mp-se/kegmon2/src_docs/source/images/ui_device_events.png

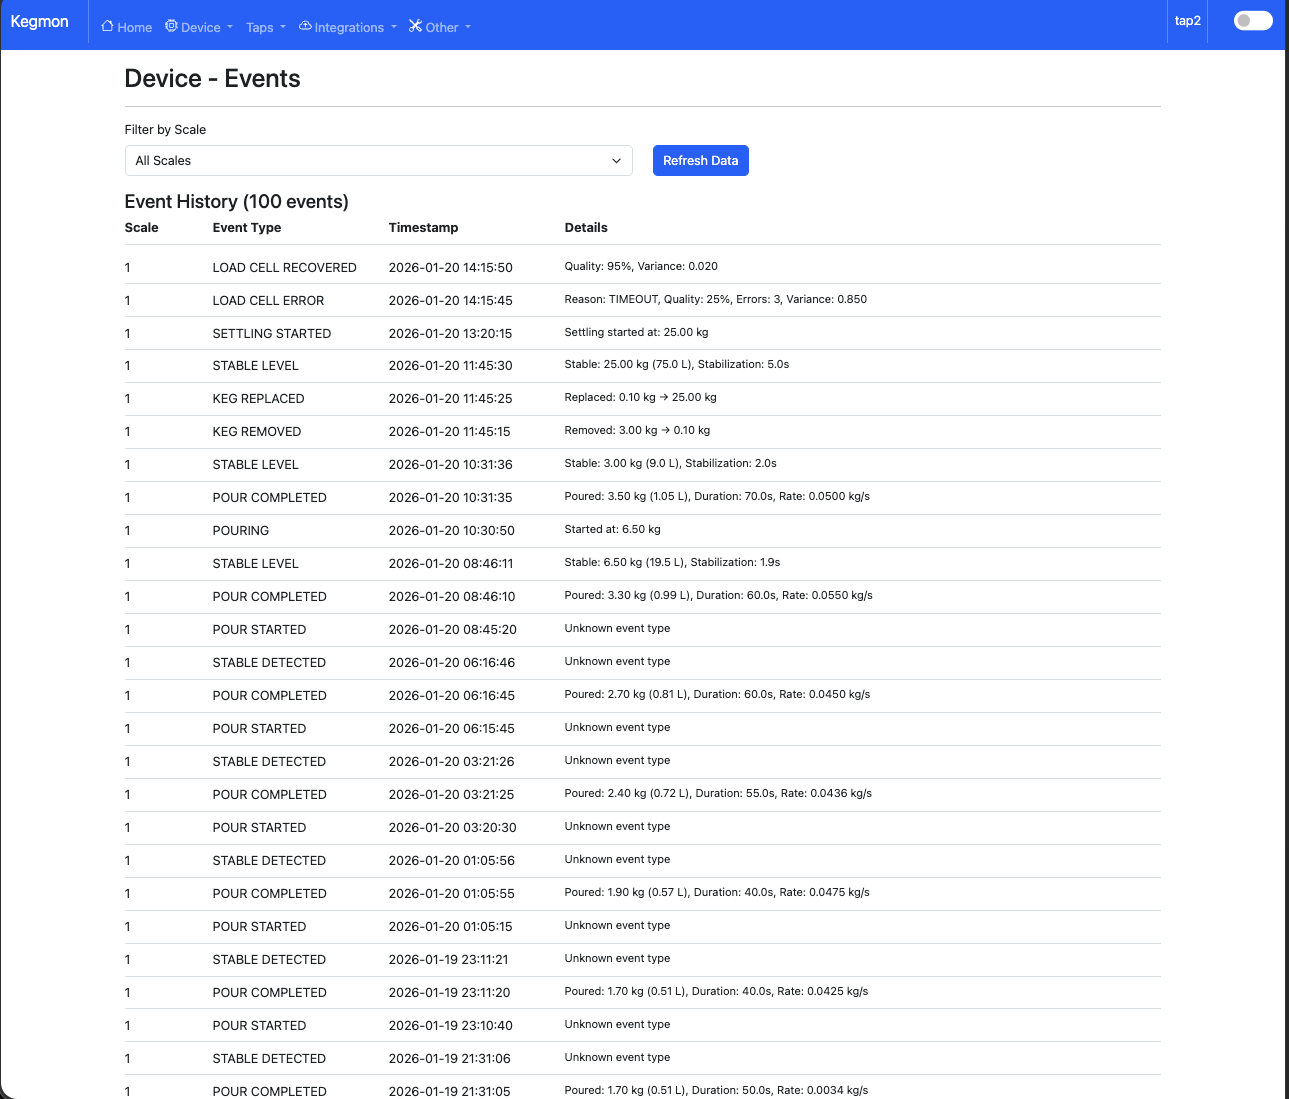
src_docs/source/images/ui_device_events.png
