mp-se/kegmon2/src_docs/source/images/ui_other_about.png

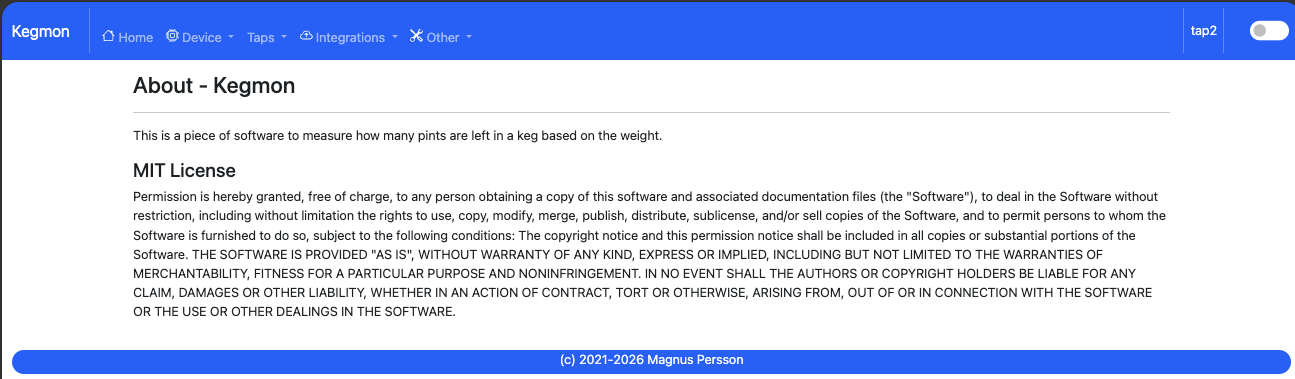
src_docs/source/images/ui_other_about.png
