mp-se/kegmon2/src/kegwebhandler.cpp

/*
 * KegMon
 * Copyright (c) 2022-2026 Magnus
 *
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
 * Alternatively, this software may be used under the terms of a
 * commercial license. See LICENSE_COMMERCIAL for details.
 *
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
 */
#include <DallasTemperature.h>
#include <OneWire.h>
#include <esp_chip_info.h>
#include <freertos/FreeRTOS.h>

#include <changedetection.hpp>
#include <kegpush.hpp>
#include <kegwebhandler.hpp>
#include <main.hpp>
#include <scale.hpp>
#include <sdcard_mmc.hpp>
#include <sdcard_sd.hpp>
#include <temp_mgr.hpp>
#include <uptime.hpp>
#include <utils.hpp>
#include <weightvolume.hpp>

// Configuration or api params
constexpr auto PARAM_APP_VER = "app_ver";
constexpr auto PARAM_APP_BUILD = "app_build";
constexpr auto PARAM_PLATFORM = "platform";
constexpr auto PARAM_BOARD = "board";
constexpr auto PARAM_CHIP_ID = "chip_id";
constexpr auto PARAM_FIRMWARE_FILE = "firmware_file";
constexpr auto PARAM_FEATURE_NO_SCALES = "no_scales";
constexpr auto PARAM_FEATURE_TFT = "tft";

// Other values
constexpr auto PARAM_TOTAL_HEAP = "total_heap";
constexpr auto PARAM_FREE_HEAP = "free_heap";
constexpr auto PARAM_IP = "ip";
constexpr auto PARAM_ADRESS = "adress";
constexpr auto PARAM_FAMILY = "family";
constexpr auto PARAM_CHIP = "chip";
constexpr auto PARAM_REVISION = "revision";
constexpr auto PARAM_CORES = "cores";
constexpr auto PARAM_FEATURES = "features";
constexpr auto PARAM_WIFI_SETUP = "wifi_setup";
constexpr auto PARAM_ONEWIRE = "onewire";

constexpr auto PARAM_UPTIME_SECONDS = "uptime_seconds";
constexpr auto PARAM_UPTIME_MINUTES = "uptime_minutes";
constexpr auto PARAM_UPTIME_HOURS = "uptime_hours";
constexpr auto PARAM_UPTIME_DAYS = "uptime_days";

// Temperature sensor parameters
constexpr auto PARAM_SENSORS = "sensors";
constexpr auto PARAM_SENSOR_INDEX = "index";
constexpr auto PARAM_SENSOR_ID = "id";
constexpr auto PARAM_SENSOR_TEMPERATURE = "temperature";

// Push status
constexpr auto PARAM_HOMEASSISTANT = "ha";
constexpr auto PARAM_BARHELPER = "barhelper";
constexpr auto PARAM_BREWSPY = "brewspy";
constexpr auto PARAM_BREWLOGGER = "brewlogger";
constexpr auto PARAM_PUSH_USED = "push_used";
constexpr auto PARAM_PUSH_AGE = "push_age";
constexpr auto PARAM_PUSH_STATUS = "push_status";
constexpr auto PARAM_PUSH_CODE = "push_code";
constexpr auto PARAM_PUSH_RESPONSE = "push_response";

// Scale parameters
constexpr auto PARAM_SCALE_INDEX = "index";
constexpr auto PARAM_STATE = "state";
constexpr auto PARAM_STABLE_WEIGHT = "stable_weight";
constexpr auto PARAM_POURING_VOLUME = "pouring_volume";
constexpr auto PARAM_LAST_POUR_VOLUME = "last_pour_volume";
constexpr auto PARAM_CONNECTED = "connected";
constexpr auto PARAM_SAMPLING_RATE = "sampling_rate";
constexpr auto PARAM_SIGNAL_QUALITY = "signal_quality";
constexpr auto PARAM_WEIGHT = "weight";
constexpr auto PARAM_SCALE = "scale_index";
constexpr auto PARAM_SCALE_BUSY = "scale_busy";
constexpr auto PARAM_RECENT_EVENTS = "recent_events";
constexpr auto PARAM_TYPE = "type";
constexpr auto PARAM_UNIT = "unit";
constexpr auto PARAM_TIMESTAMP_MS = "timestamp_ms";
constexpr auto PARAM_NAME = "name";
constexpr auto PARAM_DATA = "data";
constexpr auto PARAM_STABLE_VOLUME = "stable_volume";
constexpr auto PARAM_DURATION_MS = "duration_ms";
constexpr auto PARAM_PRE_WEIGHT = "pre_weight";
constexpr auto PARAM_POST_WEIGHT = "post_weight";
constexpr auto PARAM_VOLUME = "volume";
constexpr auto PARAM_AVG_SLOPE = "avg_slope";
constexpr auto PARAM_PREVIOUS_WEIGHT = "previous_weight";
constexpr auto PARAM_CURRENT_WEIGHT = "current_weight";
constexpr auto PARAM_EVENT_STARTUP = "startup";
constexpr auto PARAM_EVENT_SETTLING_STARTED = "settling_started";
constexpr auto PARAM_EVENT_STABLE_LEVEL = "stable_level";
constexpr auto PARAM_EVENT_POURING = "pouring";
constexpr auto PARAM_EVENT_WEIGHT_CHANGE_DETECTED = "weight_change_detected";
constexpr auto PARAM_EVENT_POUR_COMPLETED = "pour_completed";
constexpr auto PARAM_EVENT_KEG_REMOVED = "keg_removed";
constexpr auto PARAM_EVENT_KEG_REPLACED = "keg_replaced";
constexpr auto PARAM_EVENT_KEG_ABSENT_TIMEOUT = "keg_absent_timeout";
constexpr auto PARAM_EVENT_INVALID_WEIGHT = "invalid_weight";
constexpr auto PARAM_EVENT_LOAD_CELL_ERROR = "load_cell_error";
constexpr auto PARAM_EVENT_LOAD_CELL_RECOVERED = "load_cell_recovered";
constexpr auto PARAM_EVENT_SENSOR_RECOVERED = "sensor_recovered";
constexpr auto PARAM_EVENT_CALIBRATION_NEEDED = "calibration_needed";
constexpr auto PARAM_EVENT_CALIBRATION_COMPLETE = "calibration_complete";
constexpr auto PARAM_SIGNAL_REASON = "reason";
constexpr auto PARAM_VARIANCE = "variance";
constexpr auto PARAM_CONSECUTIVE_ERRORS = "consecutive_errors";
constexpr auto PARAM_INVALID_WEIGHT = "weight";
constexpr auto PARAM_MIN_VALID_WEIGHT = "min_valid_weight";
constexpr auto PARAM_MAX_VALID_WEIGHT = "max_valid_weight";
constexpr auto PARAM_SD_MOUNTED = "sd_mounted";
constexpr auto PARAM_SD = "sd";

// Forward declaration
static void eventToJson(const ChangeDetectionEvent &event, JsonObject obj);
constexpr auto PARAM_SCALE_WEIGHT = "scale_weight";
constexpr auto PARAM_SCALE_RAW = "scale_raw";
constexpr auto PARAM_GLASS = "glass";

#if defined(ENABLE_MMC)
extern SdCardMMC mySdStorage;
#elif defined(ENABLE_SD)
extern SdCardSD mySdStorage;
#endif

KegWebHandler::KegWebHandler(KegConfig *config) : BaseWebServer(config) {
  _config = config;
}

void KegWebHandler::setupWebHandlers() {
  Log.notice(F("WEB : Setting up keg web handlers." CR));

  BaseWebServer::setupWebHandlers();

  MDNS.addService("kegmon", "tcp", 80);

  // TODO(mpse) : Serve static files from SD card
  // Note! For the async implementation the order matters
  // _server->serveStatic("/levels2", LittleFS, LEVELS_FILENAME2);
  // _server->serveStatic("/levels", LittleFS, LEVELS_FILENAME);
  // _server->serveStatic("/startup", LittleFS, STARTUP_FILENAME);

  AsyncCallbackJsonWebHandler *handler;
  handler = new AsyncCallbackJsonWebHandler(
      "/api/scale/tare",
      std::bind(&KegWebHandler::webScaleTare, this, std::placeholders::_1,
                std::placeholders::_2));
  _server->addHandler(handler);
  handler = new AsyncCallbackJsonWebHandler(
      "/api/scale/factor",
      std::bind(&KegWebHandler::webScaleFactor, this, std::placeholders::_1,
                std::placeholders::_2));
  _server->addHandler(handler);
  _server->on("/api/scale", HTTP_GET, [this](AsyncWebServerRequest *request) {
    this->webScale(request);
  });
  _server->on("/api/feature", HTTP_GET, [this](AsyncWebServerRequest *request) {
    this->webFeature(request);
  });
  _server->on("/api/config", HTTP_GET, [this](AsyncWebServerRequest *request) {
    this->webConfigGet(request);
  });
  handler = new AsyncCallbackJsonWebHandler(
      "/api/config", std::bind(&KegWebHandler::webConfigPost, this,
                               std::placeholders::_1, std::placeholders::_2));
  _server->addHandler(handler);
  _server->on("/api/statistic/clear", HTTP_GET,
              [this](AsyncWebServerRequest *request) {
                this->webStatisticClear(request);
              });
  _server->on(
      "/api/statistic", HTTP_GET,
      [this](AsyncWebServerRequest *request) { this->webStatistic(request); });
  _server->on("/api/status", HTTP_GET, [this](AsyncWebServerRequest *request) {
    this->webStatus(request);
  });
  handler = new AsyncCallbackJsonWebHandler(
      "/api/brewspy/tap",
      std::bind(&KegWebHandler::webHandleBrewspy, this, std::placeholders::_1,
                std::placeholders::_2));
  _server->addHandler(handler);
  _server->on("/api/hardware/status", HTTP_GET,
              [this](AsyncWebServerRequest *request) {
                this->webHardwareScanStatus(request);
              });
  _server->on("/api/hardware", HTTP_GET,
              [this](AsyncWebServerRequest *request) {
                this->webHardwareScan(request);
              });
  _server->on("/api/factory", HTTP_GET, [this](AsyncWebServerRequest *request) {
    this->webHandleFactoryDefaults(request);
  });
  handler = new AsyncCallbackJsonWebHandler(
      "/api/sd", std::bind(&KegWebHandler::webHandleSecureDigital, this,
                           std::placeholders::_1, std::placeholders::_2));
  _server->addHandler(handler);
#if defined(ENABLE_MMC) || defined(ENABLE_SD)
  _server->serveStatic("/sd", mySdStorage.getFS(), "/");
#endif  
}

void KegWebHandler::webHandleSecureDigital(AsyncWebServerRequest *request,
                                           JsonVariant &json) {
  if (!isAuthenticated(request)) {
    return;
  }

  Log.notice(F("WEB : webServer callback for /api/sd." CR));
#if defined(ENABLE_MMC) || defined(ENABLE_SD)
  JsonObject obj = json.as<JsonObject>();

  if (!obj[PARAM_COMMAND].isNull()) {
    if (obj[PARAM_COMMAND] == String("dir")) {
      Log.notice(F("WEB : File system listing requested." CR));
      AsyncJsonResponse *response = new AsyncJsonResponse(false);
      JsonObject obj = response->getRoot().as<JsonObject>();

      obj[PARAM_TOTAL] = mySdStorage.totalBytes();
      obj[PARAM_USED] = mySdStorage.usedBytes();
      obj[PARAM_FREE] = mySdStorage.totalBytes() - mySdStorage.usedBytes();

      File root = mySdStorage.open("/", FILE_READ);
      File f = root.openNextFile();
      int i = 0;

      JsonArray arr = obj[PARAM_FILES].to<JsonArray>();
      while (f) {
        Log.notice(F("WEB : %s." CR), f.name());
        if (!String(f.name()).startsWith(
                ".")) {  // Ignore files with . (hidden files)
          arr[i][PARAM_FILE] = "/" + String(f.name());
          arr[i][PARAM_SIZE] = static_cast<int>(f.size());
          i++;
        }
        f = root.openNextFile();
      }
      f.close();
      root.close();

      response->setLength();
      request->send(response);
    } else if (obj[PARAM_COMMAND] == String("del")) {
      Log.notice(F("WEB : File system delete requested." CR));

      if (!obj[PARAM_FILE].isNull()) {
        String f = obj[PARAM_FILE];
        mySdStorage.remove(f);
        request->send(200);
      } else {
        request->send(400);
      }
    } else {
      Log.warning(F("WEB : Unknown file system command." CR));
      request->send(400);
    }
  } else {
    Log.warning(F("WEB : Unknown file system command." CR));
    request->send(400);
  }
#endif
}

void KegWebHandler::webConfigGet(AsyncWebServerRequest *request) {
  if (!isAuthenticated(request)) {
    return;
  }

  Log.notice(F("WEB : webServer callback for /api/config(read)." CR));
  AsyncJsonResponse *response = new AsyncJsonResponse(false);
  JsonObject obj = response->getRoot().as<JsonObject>();
  myConfig.createJson(obj);
  response->setLength();
  request->send(response);
}

void KegWebHandler::webHandleFactoryDefaults(AsyncWebServerRequest *request) {
  if (!isAuthenticated(request)) {
    return;
  }

  Log.notice(F("WEB : webServer callback for /api/factory." CR));
  myConfig.saveFileWifiOnly();
  LittleFS.remove(ERR_FILENAME);
  LittleFS.end();
  Log.notice(F("WEB : Deleted files in filesystem, rebooting." CR));

  AsyncJsonResponse *response = new AsyncJsonResponse(false);
  JsonObject obj = response->getRoot().as<JsonObject>();
  obj[PARAM_SUCCESS] = true;
  obj[PARAM_MESSAGE] = "Factory reset completed, rebooting";
  response->setLength();
  request->send(response);
  delay(500);
  ESP_RESET();
}

void KegWebHandler::webConfigPost(AsyncWebServerRequest *request,
                                  JsonVariant &json) {
  if (!isAuthenticated(request)) {
    return;
  }

  Log.notice(F("WEB : webServer callback for /api/config(write)." CR));
  JsonObject obj = json.as<JsonObject>();
  myConfig.parseJson(obj);
  obj.clear();
  myConfig.saveFile();

  AsyncJsonResponse *response = new AsyncJsonResponse(false);
  obj = response->getRoot().as<JsonObject>();
  obj[PARAM_SUCCESS] = true;
  obj[PARAM_MESSAGE] = "Configuration updated";
  response->setLength();
  request->send(response);
}

void KegWebHandler::webHandleBrewspy(AsyncWebServerRequest *request,
                                     JsonVariant &json) {
  if (!isAuthenticated(request)) {
    return;
  }

  JsonObject obj = json.as<JsonObject>();
  AsyncJsonResponse *response = new AsyncJsonResponse(false);
  JsonObject obj2 = response->getRoot().as<JsonObject>();
  myPush.requestTapInfoFromBrewspy(obj2, obj[PARAM_TOKEN]);
  response->setLength();
  request->send(response);
}

void KegWebHandler::webScale(AsyncWebServerRequest *request) {
  if (!isAuthenticated(request)) {
    return;
  }

  Log.notice(F("WEB : webServer callback /api/scale." CR));

  AsyncJsonResponse *response = new AsyncJsonResponse(false);
  JsonObject obj = response->getRoot().as<JsonObject>();
  obj[PARAM_WEIGHT_UNIT] = myConfig.getWeightUnit();
  obj[PARAM_VOLUME_UNIT] = myConfig.getVolumeUnit();
  obj[PARAM_TEMP_UNIT] = String(myConfig.getTempUnit());

  obj[PARAM_SCALE_BUSY] = myScale.isScheduleRunning();

  // Return array of all scales with current state
  JsonArray scales_array = obj[PARAM_SCALES].to<JsonArray>();
  for (int i = 0; i < MAX_SCALES; i++) {
    UnitIndex idx = static_cast<UnitIndex>(i);
    JsonObject scale = scales_array.add<JsonObject>();

    scale[PARAM_SCALE_INDEX] = i;
    scale[PARAM_CONNECTED] = myScale.isConnected(idx);

    scale[PARAM_SCALE_FACTOR] = myConfig.getScaleFactor(idx);
    scale[PARAM_SCALE_OFFSET] = myConfig.getScaleOffset(idx);

    // Add detected sampling rate (measured from Data Ready signal timing)
    if (myScale.isConnected(idx)) {
      uint8_t detected_rate = myScale.getSamplingRate(idx);
      if (detected_rate > 0) {
        scale[PARAM_SAMPLING_RATE] = detected_rate;
      }

      // Add signal quality for load cell connection monitoring
      uint8_t quality = myChangeDetection.getSignalQuality(idx);
      scale[PARAM_SIGNAL_QUALITY] = quality;
    }

    // Only add other data if scale is connected
    if (myScale.isConnected(idx)) {
      scale[PARAM_STATE] = myChangeDetection.getStateString(idx);

      if (!isnan(myChangeDetection.getStableWeight(idx))) {
        scale[PARAM_STABLE_WEIGHT] = myChangeDetection.getStableWeight(idx);
      }
      scale[PARAM_SCALE_RAW] = myScale.readLastRaw(idx);
    }
  }

  response->setLength();
  request->send(response);
}

void KegWebHandler::webScaleTare(AsyncWebServerRequest *request,
                                 JsonVariant &json) {
  if (!isAuthenticated(request)) {
    return;
  }

  JsonObject obj = json.as<JsonObject>();
  int i = obj[PARAM_SCALE].as<int>();

  if (i < 0 || i >= MAX_SCALES) {
    request->send(400);
    return;
  }

  Log.notice(F("WEB : webServer callback /api/scale/tare." CR));
  myScale.scheduleTare((UnitIndex)i);

  AsyncJsonResponse *response = new AsyncJsonResponse(false);
  JsonObject obj2 = response->getRoot().as<JsonObject>();
  obj2[PARAM_SUCCESS] = true;
  obj2[PARAM_MESSAGE] = "Scale tare schedule";
  response->setLength();
  request->send(response);
}

void KegWebHandler::webScaleFactor(AsyncWebServerRequest *request,
                                   JsonVariant &json) {
  if (!isAuthenticated(request)) {
    return;
  }

  JsonObject obj = json.as<JsonObject>();
  UnitIndex idx;
  float weight = obj[PARAM_WEIGHT].as<float>();

  int i = obj[PARAM_SCALE].as<int>();

  if (i < 0 || i >= MAX_SCALES) {
    request->send(400);
    return;
  }

  Log.notice(
      F("WEB : webServer callback /api/scale/factor, weight=%Fkg [%d]." CR),
      weight, i);

  myScale.scheduleFindFactor((UnitIndex)i, weight);

  AsyncJsonResponse *response = new AsyncJsonResponse(false);
  JsonObject obj2 = response->getRoot().as<JsonObject>();
  obj2[PARAM_SUCCESS] = true;
  obj2[PARAM_MESSAGE] = "Scale tare is scheduled";
  response->setLength();
  request->send(response);
}

void KegWebHandler::webFeature(AsyncWebServerRequest *request) {
  Log.notice(F("WEB : webServer callback /api/feature." CR));

  AsyncJsonResponse *response = new AsyncJsonResponse(false);
  JsonObject obj = response->getRoot().as<JsonObject>();

#if defined(ESP32S3)
  obj[PARAM_PLATFORM] = "esp32s3";
#else
#error "Undefined target"
#endif
#if defined(BOARD)
  obj[PARAM_BOARD] = BOARD;
#else
  obj[PARAM_BOARD] = "UNDEFINED";
#endif
  obj[PARAM_APP_VER] = CFG_APPVER;
  obj[PARAM_APP_BUILD] = CFG_GITREV;
  obj[PARAM_CHIP_ID] = String(ESP.getEfuseMac(), HEX);
  obj[PARAM_FIRMWARE_FILE] = CFG_FILENAMEBIN;

  int noScales = 0;
  for (int i = 0; i < MAX_SCALES; i++) {
    if (myScale.isConnected(static_cast<UnitIndex>(i))) noScales = i + 1;
  }
  obj[PARAM_FEATURE_NO_SCALES] = noScales;

#if defined(ENABLE_TFT)
  obj[PARAM_FEATURE_TFT] = true;
#else
  obj[PARAM_FEATURE_TFT] = false;
#endif
#if defined(ENABLE_MMC) || defined(ENABLE_SD)
  obj[PARAM_SD] = true;
#else
  obj[PARAM_SD] = false;
#endif
  response->setLength();
  request->send(response);
}

void KegWebHandler::webStatus(AsyncWebServerRequest *request) {
  Log.notice(F("WEB : webServer callback /api/status." CR));

  AsyncJsonResponse *response = new AsyncJsonResponse(false);
  JsonObject obj = response->getRoot().as<JsonObject>();
  obj[PARAM_MDNS] = myConfig.getMDNS();
  obj[PARAM_ID] = myConfig.getID();
  obj[PARAM_RSSI] = WiFi.RSSI();
  obj[PARAM_SSID] = myConfig.getWifiSSID(0);
  obj[PARAM_WEIGHT_UNIT] = myConfig.getWeightUnit();
  obj[PARAM_VOLUME_UNIT] = myConfig.getVolumeUnit();
  obj[PARAM_TEMP_FORMAT] = String(myConfig.getTempFormat());

  obj[PARAM_UPTIME_SECONDS] = myUptime.getSeconds();
  obj[PARAM_UPTIME_MINUTES] = myUptime.getMinutes();
  obj[PARAM_UPTIME_HOURS] = myUptime.getHours();
  obj[PARAM_UPTIME_DAYS] = myUptime.getDays();

  obj[PARAM_SCALE_BUSY] = myScale.isScheduleRunning();

#if defined(ENABLE_MMC) || defined(ENABLE_SD)
  obj[PARAM_SD_MOUNTED] = mySdStorage.hasCard();
#else
  obj[PARAM_SD_MOUNTED] = false;
#endif

  // Return array of all scales with current state
  JsonArray scales_array = obj[PARAM_SCALES].to<JsonArray>();
  for (int i = 0; i < MAX_SCALES; i++) {
    UnitIndex idx = static_cast<UnitIndex>(i);
    JsonObject scale = scales_array.add<JsonObject>();

    scale[PARAM_SCALE_INDEX] = i;
    scale[PARAM_CONNECTED] = myScale.isConnected(idx);
    // scale[PARAM_SCALE_FACTOR] = myConfig.getScaleFactor(idx);
    // scale[PARAM_SCALE_OFFSET] = myConfig.getScaleOffset(idx);

    // Add detected sampling rate (measured from Data Ready signal timing)
    uint8_t detected_rate = myScale.getSamplingRate(idx);
    if (detected_rate > 0) {
      scale[PARAM_SAMPLING_RATE] = detected_rate;
    }

    // Only add other data if scale is connected
    if (myScale.isConnected(idx)) {
      scale[PARAM_STATE] = myChangeDetection.getStateString(idx);

      // Weight and volume data (in kg and liters)
      float stableWeight = myChangeDetection.getStableWeight(idx);
      if (!isnan(stableWeight)) {
        scale[PARAM_STABLE_WEIGHT] =
            serialized(String(stableWeight, 4));
      }

      float stableVolume = myChangeDetection.getStableVolume(idx);
      if (!isnan(stableVolume)) {
        scale[PARAM_STABLE_VOLUME] =
            serialized(String(stableVolume, 4));
      }

      float pouringVolume = myChangeDetection.getPouringVolume(idx);
      scale[PARAM_POURING_VOLUME] =
          serialized(String(pouringVolume, 4));

      float lastPourVolume = myChangeDetection.getLastPourVolume(idx);
      scale[PARAM_LAST_POUR_VOLUME] =
          serialized(String(lastPourVolume, 4));

      // Keg volume in liters
      float keg_volume_liters = myConfig.getKegVolume(idx);
      scale[PARAM_KEG_VOLUME] =
          serialized(String(keg_volume_liters, 4));

      // Calculate number of glasses (glass volume from config)
      float glass_volume_liters = myConfig.getGlassVolume(idx);
      if (glass_volume_liters > 0.0f && !isnan(stableVolume) &&
          stableVolume > 0.0f) {
        // Use stableVolume directly (both in liters)
        scale[PARAM_GLASS] =
            serialized(String(stableVolume / glass_volume_liters, 1));
      }

      // scale[PARAM_SCALE_RAW] = myScale.readLastRaw(idx);
    }
  }

  // Return array of all temperature sensors
  if (myTemp.hasSensor()) {
    JsonArray sensors_array = obj[PARAM_SENSORS].to<JsonArray>();
    int sensor_count = myTemp.getSensorCount();
    for (int i = 0; i < sensor_count; i++) {
      JsonObject sensor = sensors_array.add<JsonObject>();

      sensor[PARAM_SENSOR_INDEX] = i;
      sensor[PARAM_SENSOR_ID] = myTemp.getSensorId(i);

      float temp_c = myTemp.getLastTempC(i);
      if (!isnan(temp_c)) {
        sensor[PARAM_SENSOR_TEMPERATURE] = serialized(String(temp_c, 2));
      }
    }
  }

  obj[PARAM_TOTAL_HEAP] = ESP.getHeapSize();
  obj[PARAM_FREE_HEAP] = ESP.getFreeHeap();
  obj[PARAM_IP] = WiFi.localIP().toString();
  obj[PARAM_WIFI_SETUP] = (runMode == RunMode::wifiSetupMode) ? true : false;

  // Home Assistant
  if (myConfig.hasTargetMqtt()) {
    JsonObject o = obj[PARAM_HOMEASSISTANT].to<JsonObject>();
    HomeAssist *ha = myPush.getHomeAssist();
    o[PARAM_PUSH_AGE] =
        abs(static_cast<int32_t>((millis() - ha->getLastTimeStamp())));
    o[PARAM_PUSH_STATUS] = ha->getLastStatus();
    o[PARAM_PUSH_CODE] = ha->getLastError();
    o[PARAM_PUSH_RESPONSE] = "";
    o[PARAM_PUSH_USED] = ha->hasRun();
  }

  // Bar helper
  if (strlen(myConfig.getBarhelperApiKey()) > 0) {
    JsonObject o = obj[PARAM_BARHELPER].to<JsonObject>();
    Barhelper *bar = myPush.getBarHelper();
    o[PARAM_PUSH_AGE] =
        abs(static_cast<int32_t>((millis() - bar->getLastTimeStamp())));
    o[PARAM_PUSH_STATUS] = bar->getLastStatus();
    o[PARAM_PUSH_CODE] = bar->getLastError();
    o[PARAM_PUSH_RESPONSE] = bar->getLastResponse();
    o[PARAM_PUSH_USED] = bar->hasRun();
  }

  // Brewlogger helper
  if (strlen(myConfig.getBrewLoggerUrl()) > 0) {
    JsonObject o = obj[PARAM_BREWLOGGER].to<JsonObject>();
    BrewLogger *blog = myPush.getBrewLogger();
    o[PARAM_PUSH_AGE] =
        abs(static_cast<int32_t>((millis() - blog->getLastTimeStamp())));
    o[PARAM_PUSH_STATUS] = blog->getLastStatus();
    o[PARAM_PUSH_CODE] = blog->getLastError();
    o[PARAM_PUSH_RESPONSE] = blog->getLastResponse();
    o[PARAM_PUSH_USED] = blog->hasRun();
  }

  // Brewspy
  if (strlen(myConfig.getBrewspyToken(UnitIndex::U1)) > 0 ||
      strlen(myConfig.getBrewspyToken(UnitIndex::U2)) > 0) {
    JsonObject o = obj[PARAM_BREWSPY].to<JsonObject>();
    Brewspy *brew = myPush.getBrewspy();
    o[PARAM_PUSH_AGE] =
        abs(static_cast<int32_t>((millis() - brew->getLastTimeStamp())));
    o[PARAM_PUSH_STATUS] = brew->getLastStatus();
    o[PARAM_PUSH_CODE] = brew->getLastError();
    o[PARAM_PUSH_RESPONSE] = brew->getLastResponse();
    o[PARAM_PUSH_USED] = brew->hasRun();
  }

  // Recent events from change detection
  {
    ChangeDetectionEvent recentEvents[RECENT_EVENTS_SIZE];
    size_t eventCount = 0;
    this->getRecentEvents(recentEvents, eventCount);

    JsonArray events_array = obj[PARAM_RECENT_EVENTS].to<JsonArray>();
    for (size_t i = 0; i < eventCount; i++) {
      JsonObject event_obj = events_array.add<JsonObject>();
      eventToJson(recentEvents[i], event_obj);
    }
  }

  response->setLength();
  request->send(response);
}

void KegWebHandler::webStatistic(AsyncWebServerRequest *request) {
  if (!isAuthenticated(request)) {
    return;
  }

  Log.notice(F("WEB : webServer callback /api/stability." CR));

  AsyncJsonResponse *response = new AsyncJsonResponse(false);
  JsonObject obj = response->getRoot().as<JsonObject>();

  // Level statistics array (ChangeDetection v2 statistics)
  JsonArray level_statistics = obj["level_statistics"].to<JsonArray>();
  for (int i = 0; i < MAX_SCALES; i++) {
    UnitIndex idx = static_cast<UnitIndex>(i);
    JsonObject stat = level_statistics.add<JsonObject>();

    // Basic scale info
    stat[PARAM_SCALE_INDEX] = i;
    stat[PARAM_CONNECTED] = myScale.isConnected(idx);
    stat[PARAM_STATE] = myChangeDetection.getStateString(idx);
    stat["confidence"] = myChangeDetection.getConfidence(idx);

    // Add detected sampling rate (measured from Data Ready signal timing)
    if (myScale.isConnected(idx)) {
      uint8_t detected_rate = myScale.getSamplingRate(idx);
      if (detected_rate > 0) {
        stat[PARAM_SAMPLING_RATE] = detected_rate;
      }
    }

    // Get statistics for this scale
    const auto &stats = myChangeDetection.getStatistics(idx);

    // Pour statistics (in liters)
    stat["total_pours"] = stats.totalPours;
    stat["total_pour_volume"] = stats.totalPourVolume;
    stat["avg_pour_volume"] = stats.avgPourVolume;
    stat["max_pour_volume"] = stats.maxPourVolume;
    stat["min_pour_volume"] = stats.minPourVolume;
    stat["avg_pour_duration_sec"] = stats.avgPourDurationMs / 1000.0f;

    // Keg statistics
    stat["keg_replacements"] = stats.kegReplacements;
    stat["current_keg_age_hours"] = stats.getCurrentKegAgeHours();
    stat["last_keg_weight"] = stats.lastKegWeight;

    // State machine statistics
    stat["state_transitions"] = stats.stateTransitions;
    stat["stabilization_count"] = stats.stabilizationCount;
    stat["avg_stabilization_time_ms"] = stats.avgStabilizationTimeMs;

    // Event timestamps
    stat["last_pour_time_ms"] = static_cast<uint64_t>(stats.lastPourTimeMs);
    stat["last_stable_time_ms"] = static_cast<uint64_t>(stats.lastStableTimeMs);
    stat["last_keg_removal_time_ms"] =
        static_cast<uint64_t>(stats.lastKegRemovalTimeMs);
  }

  // Scale statistics array (hardware reading statistics)
  JsonArray scale_stats = obj["scale_statistics"].to<JsonArray>();
  for (int i = 0; i < MAX_SCALES; i++) {
    JsonObject ss = scale_stats.add<JsonObject>();
    const auto &scaleStats = myScale.getStatistics(static_cast<UnitIndex>(i));

    ss[PARAM_SCALE_INDEX] = i;
    ss["total_readings"] = scaleStats.totalReadings;
    ss["valid_readings"] = scaleStats.validReadings;
    ss["invalid_readings"] = scaleStats.invalidReadings;
    ss["reading_quality"] =
        serialized(String(scaleStats.getReadingQuality(), 1));
    ss["reading_frequency"] =
        serialized(String(scaleStats.getReadingFrequency(), 2));
    ss["last_reading_time_ms"] =
        static_cast<uint64_t>(scaleStats.lastReadingTimeMs);
    ss["first_reading_time_ms"] =
        static_cast<uint64_t>(scaleStats.firstReadingTimeMs);
    ss["raw_min"] = serialized(String(scaleStats.rawMin, 0));
    ss["raw_max"] = serialized(String(scaleStats.rawMax, 0));
    ss["raw_average"] = serialized(String(scaleStats.getRawAverage(), 0));
    ss["current_variance"] = serialized(String(scaleStats.currentVariance, 2));
    ss["stable_state_variance"] =
        serialized(String(scaleStats.stableStateVariance, 2));
    ss["stable_state_samples"] = scaleStats.stableStateSamples;
    ss["calibration_drift_per_hour"] =
        serialized(String(scaleStats.calibrationDriftPerHour, 3));
  }

  response->setLength();
  request->send(response);
}

void KegWebHandler::webStatisticClear(AsyncWebServerRequest *request) {
  if (!isAuthenticated(request)) {
    return;
  }

  Log.notice(F("WEB : webServer callback /api/statistic/clear." CR));

  // Clear statistics and reset state for all scales
  for (int i = 0; i < MAX_SCALES; i++) {
    UnitIndex idx = static_cast<UnitIndex>(i);
    myChangeDetection.resetStatistics(idx);
    myScale.resetStatistics(idx);
  }

  AsyncJsonResponse *response = new AsyncJsonResponse(false);
  JsonObject obj = response->getRoot().as<JsonObject>();
  obj[PARAM_SUCCESS] = true;
  obj[PARAM_MESSAGE] = "Statistics cleared for all scales";
  response->setLength();
  request->send(response);
}

void KegWebHandler::webHardwareScan(AsyncWebServerRequest *request) {
  if (!isAuthenticated(request)) {
    return;
  }

  Log.notice(F("WEB : webServer callback for /api/hardware." CR));
  _hardwareScanTask = true;
  _hardwareScanData = "";
  AsyncJsonResponse *response = new AsyncJsonResponse(false);
  JsonObject obj = response->getRoot().as<JsonObject>();
  obj[PARAM_SUCCESS] = true;
  obj[PARAM_MESSAGE] = "Scheduled hardware scanning";
  response->setLength();
  request->send(response);
}

void KegWebHandler::webHardwareScanStatus(AsyncWebServerRequest *request) {
  if (!isAuthenticated(request)) {
    return;
  }

  Log.notice(F("WEB : webServer callback for /api/hardware/status." CR));

  if (_hardwareScanTask || !_hardwareScanData.length()) {
    AsyncJsonResponse *response = new AsyncJsonResponse(false);
    JsonObject obj = response->getRoot().as<JsonObject>();
    obj[PARAM_STATUS] = static_cast<bool>(_hardwareScanTask);
    obj[PARAM_SUCCESS] = false;
    obj[PARAM_MESSAGE] =
        _hardwareScanTask ? "Hardware scanning running" : "No scanning running";
    response->setLength();
    request->send(response);
  } else {
    request->send(200, "application/json", _hardwareScanData);
  }
}

void KegWebHandler::loop() {
  BaseWebServer::loop();

  if (_hardwareScanTask) {
    JsonDocument doc;
    JsonObject obj = doc.to<JsonObject>();
    obj[PARAM_STATUS] = false;
    obj[PARAM_SUCCESS] = true;
    obj[PARAM_MESSAGE] = "";
    Log.notice(F("WEB : Scanning hardware." CR));

    // For this we use the last value read from the scale to avoid having to
    // much communication. The value will be updated regulary second in the main
    // loop. Return array of all scales with current state
    JsonArray scales_array = obj[PARAM_SCALES].to<JsonArray>();
    for (int i = 0; i < MAX_SCALES; i++) {
      UnitIndex idx = static_cast<UnitIndex>(i);
      JsonObject scale = scales_array.add<JsonObject>();

      scale[PARAM_SCALE_INDEX] = i;
      scale[PARAM_CONNECTED] = myScale.isConnected(idx);

      // Add detected sampling rate (measured from Data Ready signal timing)
      if (myScale.isConnected(idx)) {
        uint8_t detected_rate = myScale.getSamplingRate(idx);
        if (detected_rate > 0) {
          scale[PARAM_SAMPLING_RATE] = detected_rate;
        }
      }
    }

    // Scan onewire
    JsonArray sensors_array = obj[PARAM_ONEWIRE].to<JsonArray>();

    for (int i = 0; i < myTemp.getSensorCount(); i++) {
      JsonObject sensor = sensors_array.add<JsonObject>();
      String id = myTemp.getSensorId(i);
      int type = id.length() > 2
                     ? (strtol(id.substring(0, 2).c_str(), nullptr, 16))
                     : 0;
      sensor[PARAM_SENSOR_INDEX] = i;
      sensor[PARAM_ADRESS] = id;

      switch (type) {
        case DS18S20MODEL:
          sensor[PARAM_FAMILY] = "DS18S20";
          break;
        case DS18B20MODEL:
          sensor[PARAM_FAMILY] = "DS18B20";
          break;
        case DS1822MODEL:
          sensor[PARAM_FAMILY] = "DS1822";
          break;
        case DS1825MODEL:
          sensor[PARAM_FAMILY] = "DS1825";
          break;
        case DS28EA00MODEL:
          sensor[PARAM_FAMILY] = "DS28EA00";
          break;
        default:
          sensor[PARAM_FAMILY] = String(type, HEX);
          break;
      }
    }

    JsonObject cpu = obj[PARAM_CHIP].to<JsonObject>();

    esp_chip_info_t chip_info;
    esp_chip_info(&chip_info);

    cpu[PARAM_REVISION] = chip_info.revision;
    cpu[PARAM_CORES] = chip_info.cores;

    JsonArray feature_array = cpu[PARAM_FEATURES].to<JsonArray>();

    if (chip_info.features & CHIP_FEATURE_EMB_FLASH)
      feature_array.add("embedded flash");
    if (chip_info.features & CHIP_FEATURE_WIFI_BGN)
      feature_array.add("Embedded Flash");
    if (chip_info.features & CHIP_FEATURE_EMB_FLASH)
      feature_array.add("2.4Ghz WIFI");
    if (chip_info.features & CHIP_FEATURE_BLE)
      feature_array.add("Bluetooth LE");
    if (chip_info.features & CHIP_FEATURE_BT)
      feature_array.add("Bluetooth Classic");
    if (chip_info.features & CHIP_FEATURE_IEEE802154)
      feature_array.add("IEEE 802.15.4/LR-WPAN");
    if (chip_info.features & CHIP_FEATURE_EMB_PSRAM)
      feature_array.add("Embedded PSRAM");
    switch (chip_info.model) {
      case CHIP_ESP32:
        cpu[PARAM_FAMILY] = "ESP32";
        break;
      case CHIP_ESP32S2:
        cpu[PARAM_FAMILY] = "ESP32S2";
        break;
      case CHIP_ESP32S3:
        cpu[PARAM_FAMILY] = "ESP32S3";
        break;
      case CHIP_ESP32C3:
        cpu[PARAM_FAMILY] = "ESP32C3";
        break;
      case CHIP_ESP32H2:
        cpu[PARAM_FAMILY] = "ESP32H2";
        break;
      default:
        cpu[PARAM_FAMILY] = String(chip_info.model);
        break;
    }

    serializeJson(obj, _hardwareScanData);
    Log.notice(F("WEB : Scan complete %s." CR), _hardwareScanData.c_str());
    _hardwareScanTask = false;
  }
}

void KegWebHandler::queueEvent(const ChangeDetectionEvent &event) {
  portENTER_CRITICAL(&_eventLock);

  // Store event in ringbuffer at head position
  size_t head = _eventHead.load();
  _recentEvents[head] = event;
  _eventHead.store((head + 1) % RECENT_EVENTS_SIZE);

  // Track count (max out at RECENT_EVENTS_SIZE)
  size_t count = _eventCount.load();
  if (count < RECENT_EVENTS_SIZE) {
    _eventCount.store(count + 1);
  }

  portEXIT_CRITICAL(&_eventLock);
}

void KegWebHandler::getRecentEvents(ChangeDetectionEvent *outEvents,
                                    size_t &count) {
  // Snapshot the count to ensure consistent read
  count = _eventCount.load();

  // Copy events in chronological order (oldest first)
  if (count > 0) {
    size_t startIdx = (count < RECENT_EVENTS_SIZE) ? 0 : _eventHead.load();

    for (size_t i = 0; i < count; i++) {
      size_t srcIdx = (startIdx + i) % RECENT_EVENTS_SIZE;
      outEvents[i] = _recentEvents[srcIdx];
    }
  }
}

// Convert ChangeDetectionEvent to JSON
static void eventToJson(const ChangeDetectionEvent &event, JsonObject obj) {
  // Base event fields
  obj[PARAM_TYPE] = static_cast<int>(event.type);
  obj[PARAM_UNIT] = static_cast<int>(event.unitIndex);
  obj[PARAM_TIMESTAMP_MS] = static_cast<uint32_t>(event.timestampMs);

  // Event-specific data
  switch (event.type) {
    case ChangeDetectionEventType::SYSTEM_STARTUP:
      obj[PARAM_NAME] = PARAM_EVENT_STARTUP;
      break;

    case ChangeDetectionEventType::STABLE_LEVEL:
      obj[PARAM_NAME] = PARAM_EVENT_STABLE_LEVEL;
      {
        JsonObject stable = obj[PARAM_DATA].to<JsonObject>();
        stable[PARAM_STABLE_WEIGHT] =
            serialized(String(event.stable.stableWeightKg, 4));
        WeightVolumeConverter volumeConverter(event.unitIndex);
        float stableVolume = volumeConverter.weightToVolume(event.stable.stableWeightKg);
        stable[PARAM_STABLE_VOLUME] =
            serialized(String(stableVolume, 4));
        stable[PARAM_DURATION_MS] =
            static_cast<uint32_t>(event.stable.durationMs);
      }
      break;

    case ChangeDetectionEventType::POURING:
      obj[PARAM_NAME] = PARAM_EVENT_POURING;
      {
        JsonObject pour = obj[PARAM_DATA].to<JsonObject>();
        pour[PARAM_PRE_WEIGHT] =
            serialized(String(event.pour.prePourWeightKg, 4));
      }
      break;

    case ChangeDetectionEventType::POUR_COMPLETED:
      obj[PARAM_NAME] = PARAM_EVENT_POUR_COMPLETED;
      {
        JsonObject pour = obj[PARAM_DATA].to<JsonObject>();
        pour[PARAM_PRE_WEIGHT] =
            serialized(String(event.pour.prePourWeightKg, 4));
        pour[PARAM_POST_WEIGHT] =
            serialized(String(event.pour.postPourWeightKg, 4));
        pour[PARAM_WEIGHT] = serialized(String(event.pour.pourWeightKg, 4));
        pour[PARAM_VOLUME] = serialized(String(event.pour.pourVolumeL, 4));
        pour[PARAM_DURATION_MS] = static_cast<uint32_t>(event.pour.durationMs);
        pour[PARAM_AVG_SLOPE] =
            serialized(String(event.pour.averageSlopeKgSec, 6));
      }
      break;

    case ChangeDetectionEventType::KEG_REMOVED:
      obj[PARAM_NAME] = PARAM_EVENT_KEG_REMOVED;
      {
        JsonObject weight = obj[PARAM_DATA].to<JsonObject>();
        weight[PARAM_PREVIOUS_WEIGHT] =
            serialized(String(event.weight.previousWeightKg, 4));
        weight[PARAM_CURRENT_WEIGHT] =
            serialized(String(event.weight.currentWeightKg, 4));
      }
      break;

    case ChangeDetectionEventType::KEG_REPLACED:
      obj[PARAM_NAME] = PARAM_EVENT_KEG_REPLACED;
      {
        JsonObject weight = obj[PARAM_DATA].to<JsonObject>();
        weight[PARAM_PREVIOUS_WEIGHT] =
            serialized(String(event.weight.previousWeightKg, 4));
        weight[PARAM_CURRENT_WEIGHT] =
            serialized(String(event.weight.currentWeightKg, 4));
      }
      break;

    case ChangeDetectionEventType::INVALID_WEIGHT:
      obj[PARAM_NAME] = PARAM_EVENT_INVALID_WEIGHT;
      break;

    case ChangeDetectionEventType::LOAD_CELL_ERROR:
      obj[PARAM_NAME] = PARAM_EVENT_LOAD_CELL_ERROR;
      {
        JsonObject loadCell = obj[PARAM_DATA].to<JsonObject>();
        loadCell[PARAM_SIGNAL_REASON] =
            static_cast<uint8_t>(event.loadCell.reason);
        loadCell[PARAM_SIGNAL_QUALITY] = event.loadCell.signalQualityPercent;
        loadCell[PARAM_VARIANCE] =
            serialized(String(event.loadCell.varianceKg, 4));
        loadCell[PARAM_CONSECUTIVE_ERRORS] = event.loadCell.consecutiveErrors;
      }
      break;

    case ChangeDetectionEventType::LOAD_CELL_RECOVERED:
      obj[PARAM_NAME] = PARAM_EVENT_LOAD_CELL_RECOVERED;
      {
        JsonObject loadCell = obj[PARAM_DATA].to<JsonObject>();
        loadCell[PARAM_SIGNAL_QUALITY] = event.loadCell.signalQualityPercent;
        loadCell[PARAM_VARIANCE] =
            serialized(String(event.loadCell.varianceKg, 4));
      }
      break;

    case ChangeDetectionEventType::CALIBRATION_NEEDED:
      obj[PARAM_NAME] = PARAM_EVENT_CALIBRATION_NEEDED;
      break;

    case ChangeDetectionEventType::SETTLING_STARTED:
      obj[PARAM_NAME] = PARAM_EVENT_SETTLING_STARTED;
      break;

    case ChangeDetectionEventType::WEIGHT_CHANGE_DETECTED:
      obj[PARAM_NAME] = PARAM_EVENT_WEIGHT_CHANGE_DETECTED;
      break;

    case ChangeDetectionEventType::KEG_ABSENT_TIMEOUT:
      obj[PARAM_NAME] = PARAM_EVENT_KEG_ABSENT_TIMEOUT;
      break;

    case ChangeDetectionEventType::SENSOR_RECOVERED:
      obj[PARAM_NAME] = PARAM_EVENT_SENSOR_RECOVERED;
      break;

    case ChangeDetectionEventType::CALIBRATION_COMPLETE:
      obj[PARAM_NAME] = PARAM_EVENT_CALIBRATION_COMPLETE;
      break;
  }
}

// EOF
