mp-se/kegmon2/src/homeassist.cpp

/*
 * KegMon
 * Copyright (c) 2022-2026 Magnus
 *
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
 * Alternatively, this software may be used under the terms of a
 * commercial license. See LICENSE_COMMERCIAL for details.
 *
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
 */
#include <homeassist.hpp>
#include <kegconfig.hpp>
#include <log.hpp>
#include <scale.hpp>
#include <templating.hpp>
#include <utils.hpp>

const char *volumeTemplate =
    "kegmon/${mdns}_volume${tap}/state:${volume}|"
    "kegmon/${mdns}_volume${tap}/"
    "attr:{\"glasses\":${glasses},\"keg_volume\":${keg-volume},\"glass_"
    "volume\":${glass-volume},\"keg_percent\":${keg-percent},\"temp\":${temp},\"temp_unit\":\"${temp-format}\"}|"
    "homeassistant/sensor/${mdns}_volume${tap}/"
    "config:{\"device_class\":\"volume\",\"name\":\"${mdns}_volume${tap}\","
    "\"unit_of_measurement\":\"L\",\"state_topic\":\"kegmon/"
    "${mdns}_volume${tap}/state\",\"json_attributes_topic\":\"kegmon/"
    "${mdns}_volume${tap}/"
    "attr\",\"unique_id\":\"${mdns}_volume${tap}\","
    "\"device\": { \"identifiers\": \"${mdns}_${id}\", \"name\": \"${mdns}\", "
    "\"model\": \"kegmon\", \"manufacturer\": \"mp-se\", \"sw_version\": "
    "\"${sw-ver}\" } }|"
    "kegmon/${mdns}_temp${tap}/state:${temp}|"
    "homeassistant/sensor/${mdns}_temp${tap}/config:"
    "{\"device_class\":\"temperature\",\"name\":\"${mdns}_temp${tap}\",\"unit_of_"
    "measurement\":\"${temp-format}\",\"state_topic\":\"kegmon/"
    "${mdns}_temp${tap}/state\",\"unique_id\":\"${mdns}_temp${tap}\", "
    "\"device\": { \"identifiers\": \"${mdns}_${id}\", \"name\": \"${mdns}\", "
    "\"model\": \"kegmon\", \"manufacturer\": \"mp-se\", \"sw_version\": "
    "\"${sw-ver}\" } }|";

const char *beerTemplate =
    "kegmon/${mdns}_beer${tap}/state:${beer-name}|"
    "kegmon/${mdns}_beer${tap}/"
    "attr:{\"abv\":${beer-abv},\"abv\":${beer-abv},\"ibu\":${beer-ibu},\"ebc\":"
    "${beer-"
    "ebc}}|"
    "homeassistant/sensor/${mdns}_beer${tap}/config:"
    "{\"name\":\"${mdns}_beer${tap}\",\"state_topic\":\"kegmon/"
    "${mdns}_beer${tap}/state\",\"json_attributes_topic\":\"kegmon/"
    "${mdns}_beer${tap}/"
    "attr\",\"unique_id\":\"${mdns}_beer${tap}\","
    "\"device\": { \"identifiers\": \"${mdns}_${id}\", \"name\": \"${mdns}\", "
    "\"model\": \"kegmon\", \"manufacturer\": \"mp-se\", \"sw_version\": "
    "\"${sw-ver}\" } }|";

const char *pourTemplate =
    "kegmon/${mdns}_pour${tap}/state:${pour}|"
    "kegmon/${mdns}_pour${tap}/"
    "attr:{\"temp\":${temp},\"temp_unit\":\"${temp-format}\"}|"
    "homeassistant/sensor/${mdns}_pour${tap}/config:"
    "{\"device_class\":\"volume\",\"name\":\"${mdns}_pour${tap}\",\"unit_of_"
    "measurement\":\"L\",\"state_topic\":\"kegmon/"
    "${mdns}_pour${tap}/state\",\"json_attributes_topic\":\"kegmon/"
    "${mdns}_pour${tap}/attr\",\"unique_id\":\"${mdns}_pour${tap}\", "
    "\"device\": { \"identifiers\": \"${mdns}_${id}\", \"name\": \"${mdns}\", "
    "\"model\": \"kegmon\", \"manufacturer\": \"mp-se\", \"sw_version\": "
    "\"${sw-ver}\" } }|"
    "kegmon/${mdns}_temp${tap}/state:${temp}|"
    "homeassistant/sensor/${mdns}_temp${tap}/config:"
    "{\"device_class\":\"temperature\",\"name\":\"${mdns}_temp${tap}\",\"unit_of_"
    "measurement\":\"${temp-format}\",\"state_topic\":\"kegmon/"
    "${mdns}_temp${tap}/state\",\"unique_id\":\"${mdns}_temp${tap}\", "
    "\"device\": { \"identifiers\": \"${mdns}_${id}\", \"name\": \"${mdns}\", "
    "\"model\": \"kegmon\", \"manufacturer\": \"mp-se\", \"sw_version\": "
    "\"${sw-ver}\" } }|";

const char *stateTemplate =
    "kegmon/${mdns}_state${tap}/state:${state}|"
    "homeassistant/sensor/${mdns}_state${tap}/config:"
    "{\"name\":\"${mdns}_state${tap}\",\"state_topic\":\"kegmon/"
    "${mdns}_state${tap}/state\",\"unique_id\":\"${mdns}_state${tap}\", "
    "\"device\": { \"identifiers\": \"${mdns}_${id}\", \"name\": \"${mdns}\", "
    "\"model\": \"kegmon\", \"manufacturer\": \"mp-se\", \"sw_version\": "
    "\"${sw-ver}\" } }|";

void HomeAssist::sendTapInformation(UnitIndex idx, float stableVol,
                                    float glasses, float tempC) {
  if (!myConfig.hasTargetMqtt()) return;

  TemplatingEngine tpl;

  tpl.setVal("${mdns}", myConfig.getMDNS());
  tpl.setVal("${sw-ver}", CFG_APPVER);
  tpl.setVal("${id}", myConfig.getID());
  tpl.setVal("${volume}", stableVol, 3);
  tpl.setVal("${glasses}", glasses, 1);
  tpl.setVal("${tap}", static_cast<int>(idx) + 1);
  tpl.setVal("${beer-name}", myConfig.getBeerName(idx));
  tpl.setVal("${beer-abv}", myConfig.getBeerABV(idx));
  tpl.setVal("${beer-ibu}", myConfig.getBeerIBU(idx));
  tpl.setVal("${beer-ebc}", myConfig.getBeerEBC(idx));

  tpl.setVal("${keg-volume}", myConfig.getKegVolume(idx));
  tpl.setVal("${glass-volume}", myConfig.getGlassVolume(idx));
  tpl.setVal("${keg-percent}", (stableVol / myConfig.getKegVolume(idx)) * 100);
  if (!isnan(tempC)) {
    tpl.setVal("${temp}", tempC, 2);
  } else {
    tpl.setVal("${temp}", "null");
  }
  tpl.setVal("${temp-format}", "°C");

  const char *out = tpl.create(volumeTemplate);
  EspSerial.print(out);
  EspSerial.print(CR);
  String outStr(out);
  _push->sendMqtt(outStr);
  updateStatus();

  Log.notice(F("HA  : Sending TAP information to HA, last %Fl [%d]" CR),
             stableVol);

  out = tpl.create(beerTemplate);
  EspSerial.print(out);
  EspSerial.print(CR);
  outStr = out;
  _push->sendMqtt(outStr);
  updateStatus();

  tpl.freeMemory();
}

void HomeAssist::sendPourInformation(UnitIndex idx, float pourVol, float tempC) {
  if (!myConfig.hasTargetMqtt()) return;

  TemplatingEngine tpl;

  tpl.setVal("${mdns}", myConfig.getMDNS());
  tpl.setVal("${sw-ver}", CFG_APPVER);
  tpl.setVal("${id}", myConfig.getID());
  tpl.setVal("${pour}", pourVol, 3);
  tpl.setVal("${tap}", static_cast<int>(idx) + 1);
  if (!isnan(tempC)) {
    tpl.setVal("${temp}", tempC, 2);
  } else {
    tpl.setVal("${temp}", "null");
  }
  tpl.setVal("${temp-format}", "°C");

  Log.notice(F("HA  : Sending POUR information to HA, pour %Fl [%d]." CR),
             pourVol, idx);

  const char *out = tpl.create(pourTemplate);
  EspSerial.print(out);
  EspSerial.print(CR);
  String outStr(out);
  _push->sendMqtt(outStr);
  updateStatus();

  tpl.freeMemory();
}

void HomeAssist::sendEventState(UnitIndex idx,
                                 ChangeDetectionEventType eventType) {
  if (!myConfig.hasTargetMqtt()) return;

  TemplatingEngine tpl;

  tpl.setVal("${mdns}", myConfig.getMDNS());
  tpl.setVal("${sw-ver}", CFG_APPVER);
  tpl.setVal("${id}", myConfig.getID());
  tpl.setVal("${state}", getEventTypeDisplayName(eventType));
  tpl.setVal("${tap}", static_cast<int>(idx) + 1);

  Log.notice(F("HA  : Sending EVENT STATE to HA: %s [%d]" CR),
             getEventTypeDisplayName(eventType), idx);

  const char *out = tpl.create(stateTemplate);
  EspSerial.print(out);
  EspSerial.print(CR);
  String outStr(out);
  _push->sendMqtt(outStr);
  updateStatus();

  tpl.freeMemory();
}

void HomeAssist::updateStatus() {
  _lastTimestamp = millis();
  _lastStatus = _push->wasLastSuccessful();
  _lastMqttError = _push->getLastResponseCode();
  _hasRun = true;
}

// EOF
