mp-se/kegmon2/src/kegconfig.cpp

/*
 * KegMon
 * Copyright (c) 2022-2026 Magnus
 *
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
 * Alternatively, this software may be used under the terms of a
 * commercial license. See LICENSE_COMMERCIAL for details.
 *
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
 */
#include <kegconfig.hpp>
#include <log.hpp>
#include <main.hpp>
#include <utils.hpp>

KegConfig::KegConfig(String baseMDNS, String fileName)
    : BaseConfig(baseMDNS, fileName) {}

void KegConfig::createJson(JsonObject& doc) const {
  // Call base class functions
  createJsonBase(doc);
  createJsonWifi(doc);
  createJsonOta(doc);
  createJsonPush(doc);

  // Handle project specific config
  doc[PARAM_WEIGHT_UNIT] = getWeightUnit();
  doc[PARAM_VOLUME_UNIT] = getVolumeUnit();
  doc[PARAM_DISPLAY_LAYOUT] = getDisplayLayoutTypeAsInt();
  doc[PARAM_BREWFATHER_APIKEY] = getBrewfatherApiKey();
  doc[PARAM_BREWFATHER_USERKEY] = getBrewfatherUserKey();
  doc[PARAM_BREWLOGGER_URL] = getBrewLoggerUrl();

  // Brewspy tokens as array
  JsonArray brewspy = doc[PARAM_BREWSPY_TOKENS].to<JsonArray>();
  for (int i = 0; i < MAX_SCALES; i++) {
    brewspy.add(getBrewspyToken(static_cast<UnitIndex>(i)));
  }

  doc[PARAM_BARHELPER_APIKEY] = getBarhelperApiKey();

  // Barhelper monitors as array
  JsonArray barhelper_monitors = doc[PARAM_BARHELPER_MONITORS].to<JsonArray>();
  for (int i = 0; i < MAX_SCALES; i++) {
    barhelper_monitors.add(getBarhelperMonitor(static_cast<UnitIndex>(i)));
  }

  // Save scale and beer data as arrays
  JsonArray scales = doc[PARAM_SCALES].to<JsonArray>();
  for (int i = 0; i < MAX_SCALES; i++) {
    UnitIndex idx = static_cast<UnitIndex>(i);
    JsonObject scale = scales.add<JsonObject>();

    scale[PARAM_SCALE_FACTOR] = serialized(String(getScaleFactor(idx), 5));
    scale[PARAM_SCALE_OFFSET] = getScaleOffset(idx);
    scale[PARAM_KEG_WEIGHT] =
        serialized(String(getKegWeight(idx), getWeightPrecision()));
    scale[PARAM_KEG_VOLUME] =
        serialized(String(getKegVolume(idx), getWeightPrecision()));
    scale[PARAM_GLASS_VOLUME] =
        serialized(String(getGlassVolume(idx), getWeightPrecision()));
    scale[PARAM_TEMP_SENSOR_ID] = getTempSensorId(idx);
  }

  // Save beer data as arrays
  JsonArray beers = doc[PARAM_BEERS].to<JsonArray>();
  for (int i = 0; i < MAX_SCALES; i++) {
    UnitIndex idx = static_cast<UnitIndex>(i);
    JsonObject beer = beers.add<JsonObject>();

    beer[PARAM_BEER_NAME] = getBeerName(idx);
    beer[PARAM_BEER_ID] = getBeerId(idx);
    beer[PARAM_BEER_ABV] = serialized(String(getBeerABV(idx), 1));
    beer[PARAM_BEER_FG] = serialized(String(getBeerFG(idx), 4));
    beer[PARAM_BEER_EBC] = getBeerEBC(idx);
    beer[PARAM_BEER_IBU] = getBeerIBU(idx);
  }
}

void KegConfig::parseJson(JsonObject& doc) {
  // Call base class functions
  parseJsonBase(doc);
  parseJsonWifi(doc);
  parseJsonOta(doc);
  parseJsonPush(doc);

  // Handle project specific config
  if (!doc[PARAM_WEIGHT_UNIT].isNull()) setWeightUnit(doc[PARAM_WEIGHT_UNIT]);
  if (!doc[PARAM_VOLUME_UNIT].isNull()) setVolumeUnit(doc[PARAM_VOLUME_UNIT]);

  if (!doc[PARAM_BREWFATHER_APIKEY].isNull())
    setBrewfatherApiKey(doc[PARAM_BREWFATHER_APIKEY]);
  if (!doc[PARAM_BREWFATHER_USERKEY].isNull())
    setBrewfatherUserKey(doc[PARAM_BREWFATHER_USERKEY]);

  if (!doc[PARAM_BREWLOGGER_URL].isNull())
    setBrewLoggerUrl(doc[PARAM_BREWLOGGER_URL]);

  // Load brewspy tokens from array
  if (!doc[PARAM_BREWSPY_TOKENS].isNull()) {
    JsonArray brewspy = doc[PARAM_BREWSPY_TOKENS].as<JsonArray>();
    for (int i = 0; i < MAX_SCALES && i < static_cast<int>(brewspy.size());
         i++) {
      if (!brewspy[i].isNull()) {
        setBrewspyToken(static_cast<UnitIndex>(i), brewspy[i].as<String>());
      }
    }
  }

  if (!doc[PARAM_BARHELPER_APIKEY].isNull())
    setBarhelperApiKey(doc[PARAM_BARHELPER_APIKEY]);

  // Load barhelper monitors from array
  if (!doc[PARAM_BARHELPER_MONITORS].isNull()) {
    JsonArray monitors = doc[PARAM_BARHELPER_MONITORS].as<JsonArray>();
    for (int i = 0; i < MAX_SCALES && i < static_cast<int>(monitors.size());
         i++) {
      if (!monitors[i].isNull()) {
        setBarhelperMonitor(static_cast<UnitIndex>(i),
                            monitors[i].as<String>());
      }
    }
  }

  if (!doc[PARAM_DISPLAY_LAYOUT].isNull())
    setDisplayLayoutType(doc[PARAM_DISPLAY_LAYOUT].as<int>());

  // Load scale data from array
  if (!doc[PARAM_SCALES].isNull()) {
    JsonArray scales = doc[PARAM_SCALES].as<JsonArray>();
    for (int i = 0; i < MAX_SCALES && i < static_cast<int>(scales.size());
         i++) {
      UnitIndex idx = static_cast<UnitIndex>(i);
      JsonObject scale = scales[i].as<JsonObject>();

      if (!scale[PARAM_SCALE_FACTOR].isNull())
        setScaleFactor(idx, scale[PARAM_SCALE_FACTOR].as<float>());
      if (!scale[PARAM_SCALE_OFFSET].isNull())
        setScaleOffset(idx, scale[PARAM_SCALE_OFFSET].as<float>());
      if (!scale[PARAM_KEG_WEIGHT].isNull())
        setKegWeight(idx, scale[PARAM_KEG_WEIGHT].as<float>());
      if (!scale[PARAM_KEG_VOLUME].isNull())
        setKegVolume(idx, scale[PARAM_KEG_VOLUME].as<float>());
      if (!scale[PARAM_GLASS_VOLUME].isNull())
        setGlassVolume(idx, scale[PARAM_GLASS_VOLUME].as<float>());
      if (!scale[PARAM_TEMP_SENSOR_ID].isNull())
        setTempSensorId(idx, scale[PARAM_TEMP_SENSOR_ID].as<String>());
    }
  }

  // Load beer data from array
  if (!doc[PARAM_BEERS].isNull()) {
    JsonArray beers = doc[PARAM_BEERS].as<JsonArray>();
    for (int i = 0; i < MAX_SCALES && i < static_cast<int>(beers.size()); i++) {
      UnitIndex idx = static_cast<UnitIndex>(i);
      JsonObject beer = beers[i].as<JsonObject>();

      if (!beer[PARAM_BEER_NAME].isNull())
        setBeerName(idx, beer[PARAM_BEER_NAME]);
      if (!beer[PARAM_BEER_ID].isNull()) setBeerId(idx, beer[PARAM_BEER_ID]);
      if (!beer[PARAM_BEER_EBC].isNull())
        setBeerEBC(idx, beer[PARAM_BEER_EBC].as<int>());
      if (!beer[PARAM_BEER_ABV].isNull())
        setBeerABV(idx, beer[PARAM_BEER_ABV].as<float>());
      if (!beer[PARAM_BEER_IBU].isNull())
        setBeerIBU(idx, beer[PARAM_BEER_IBU].as<int>());
      if (!beer[PARAM_BEER_FG].isNull())
        setBeerFG(idx, beer[PARAM_BEER_FG].as<float>());
    }
  }
}

// EOF
