mp-se/kegmon2/src/event_logger.hpp

/*
 * KegMon
 * Copyright (c) 2022-2026 Magnus
 *
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
 * Alternatively, this software may be used under the terms of a
 * commercial license. See LICENSE_COMMERCIAL for details.
 *
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
 */
#ifndef SRC_EVENT_LOGGER_HPP_
#define SRC_EVENT_LOGGER_HPP_

#include <changedetection.hpp>
#include <cstdint>
#include <sdcard_mmc.hpp>
#include <sdcard_sd.hpp>
#include <weightvolume.hpp>

// CSV log versioning for schema evolution
#define LOG_VERSION 1

// File rotation configuration
#define MAX_LOG_FILE_SIZE (16 * 1024)  // 16KB
#define MAX_LOG_FILES 4
#define LOG_BASE_FILENAME "/data"
#define LOG_FILE_EXTENSION ".csv"

/**
 * SD Card Event Logger
 * Logs all change detection events to CSV format on SD card
 * Each row includes a version number for schema compatibility
 * File rotation: data.csv -> data1.csv -> data2.csv -> data3.csv (drops oldest)
 */
class EventLogger {
 public:
  EventLogger() = default;
  ~EventLogger() = default;

  /**
   * Initialize the logger
   * Sets up baseline timestamp from system startup
   */
  void init();

  /**
   * Log a single event to CSV
   * Formats event with version, timestamp, and all event-specific data
   * Performs file rotation if threshold exceeded
   */
  void logEvent(const ChangeDetectionEvent& event);

 private:
  // Timestamp baseline (milliseconds from SYSTEM_STARTUP event)
  uint64_t _systemStartupMs = 0;

  // Track if we've written the baseline SYSTEM_STARTUP event
  bool _startupLogged = false;

  /**
   * Check if SD card is present and accessible
   */
  bool hasCard() const;

  /**
   * Get full path to current log file
   */
  const char* getCurrentLogPath() const;

  /**
   * Get full path to log file by index (0 = data.csv, 1 = data1.csv, etc.)
   */
  void getLogPathByIndex(int index, char* buffer, size_t bufferSize) const;

  /**
   * Format timestamp from event
   * Uses RTC time with millisecond offset from SYSTEM_STARTUP baseline
   */
  void formatTimestamp(const ChangeDetectionEvent& event, char* buffer,
                       size_t bufferSize);

  /**
   * Get event type as string
   */
  const char* getEventTypeString(ChangeDetectionEventType type) const;

  /**
   * Format event data as CSV row
   * Includes version number as first column
   */
  void formatEventRow(const ChangeDetectionEvent& event, char* buffer,
                      size_t bufferSize);

  /**
   * Check if current log file should be rotated
   */
  bool shouldRotate() const;

  /**
   * Perform file rotation
   * data3.csv deleted, data2->data3, data1->data2, data->data1
   */
  void rotateFiles();

  /**
   * Write row to current log file
   * Creates file if it doesn't exist
   */
  void writeToFile(const char* row);
};

extern EventLogger myEventLogger;

#endif  // SRC_EVENT_LOGGER_HPP_
